lucidm/i2lcd/pictures/6x1.jpg

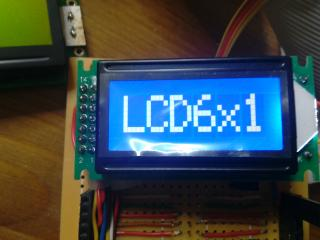
pictures/6x1.jpg
