lucidm/i2lcd/pictures/12x4.jpg

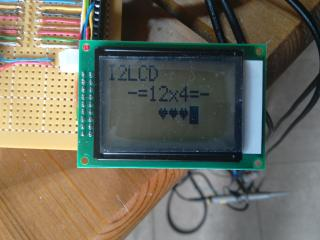
pictures/12x4.jpg
