lucidm/i2lcd/pictures/16x1.jpg

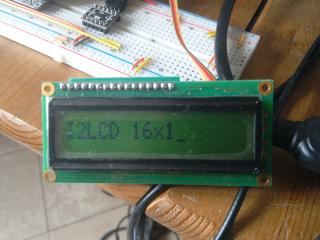
pictures/16x1.jpg
