lucidm/i2lcd/pictures/16x2.jpg

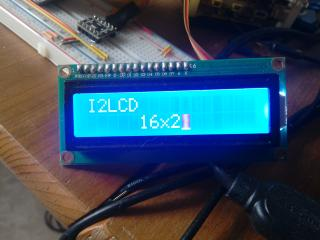
pictures/16x2.jpg
