lucidm/i2lcd/pictures/16x4.jpg

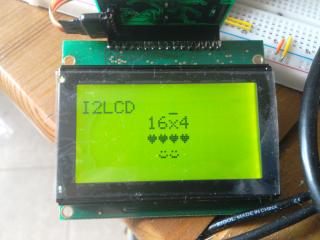
pictures/16x4.jpg
