lucidm/i2lcd/pictures/20x4.jpg

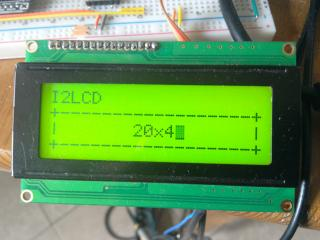
pictures/20x4.jpg
