lucidm/i2lcd/pictures/24x2.jpg

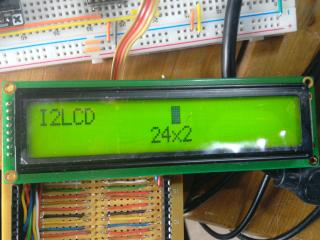
pictures/24x2.jpg
