lucidm/i2lcd/pictures/anano-fritz1.png

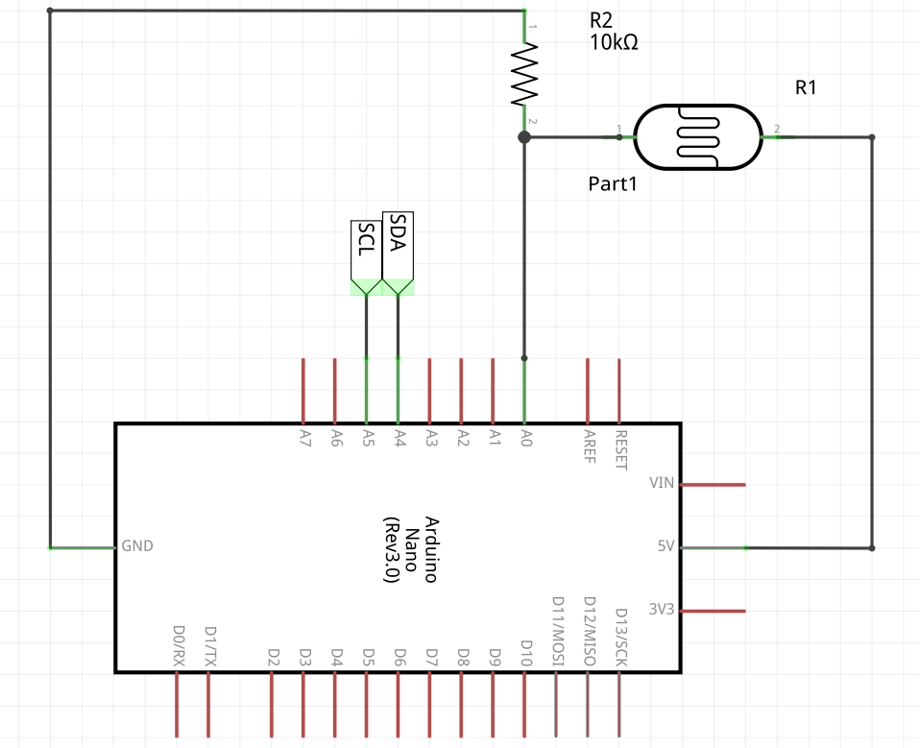
pictures/anano-fritz1.png
