lucidm/i2lcd/pictures/anano-fritz.png

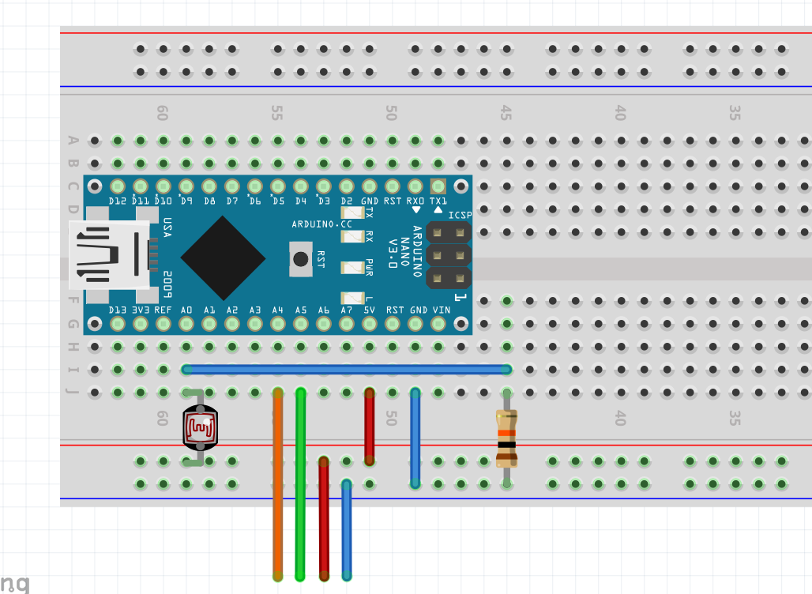
pictures/anano-fritz.png
