lucidm/i2lcd/pictures/backlight-connections4.png

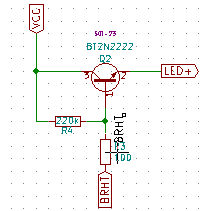
pictures/backlight-connections4.png
