lucidm/i2lcd/pictures/busyflagcir-connections5.png

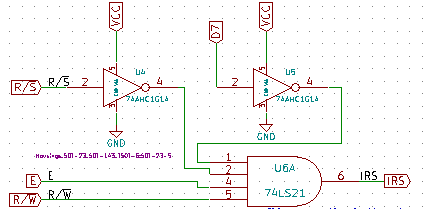
pictures/busyflagcir-connections5.png
