lucidm/i2lcd/pictures/kicad_pcb.png

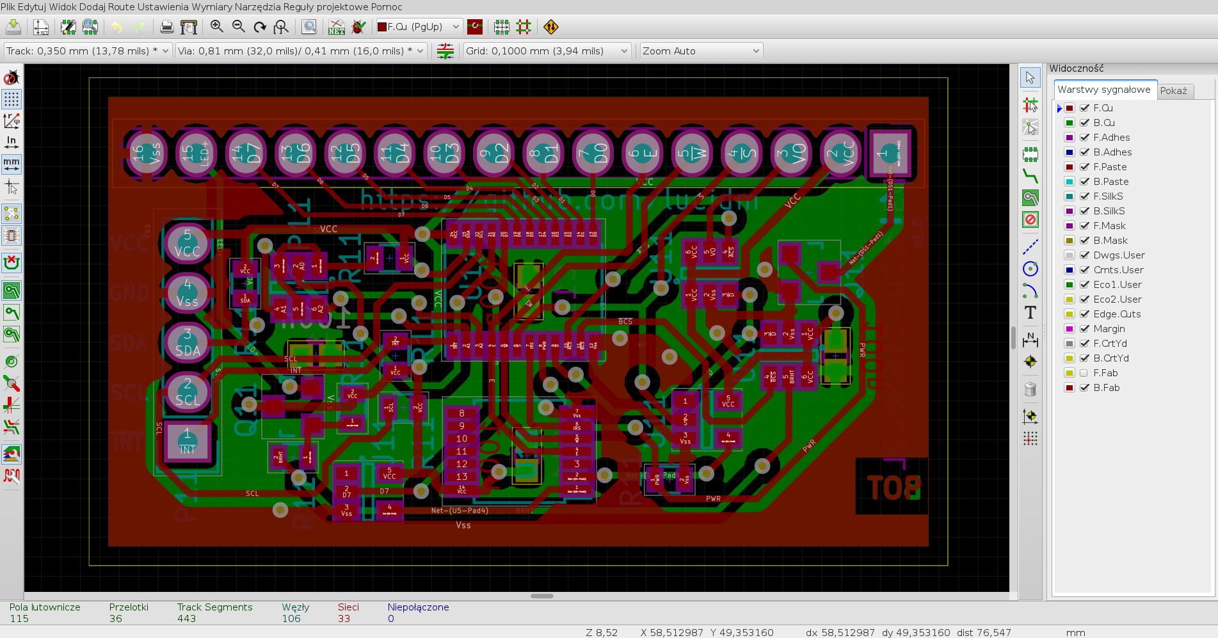
pictures/kicad_pcb.png
