lucidm/i2lcd/pictures/kicad_sch.png

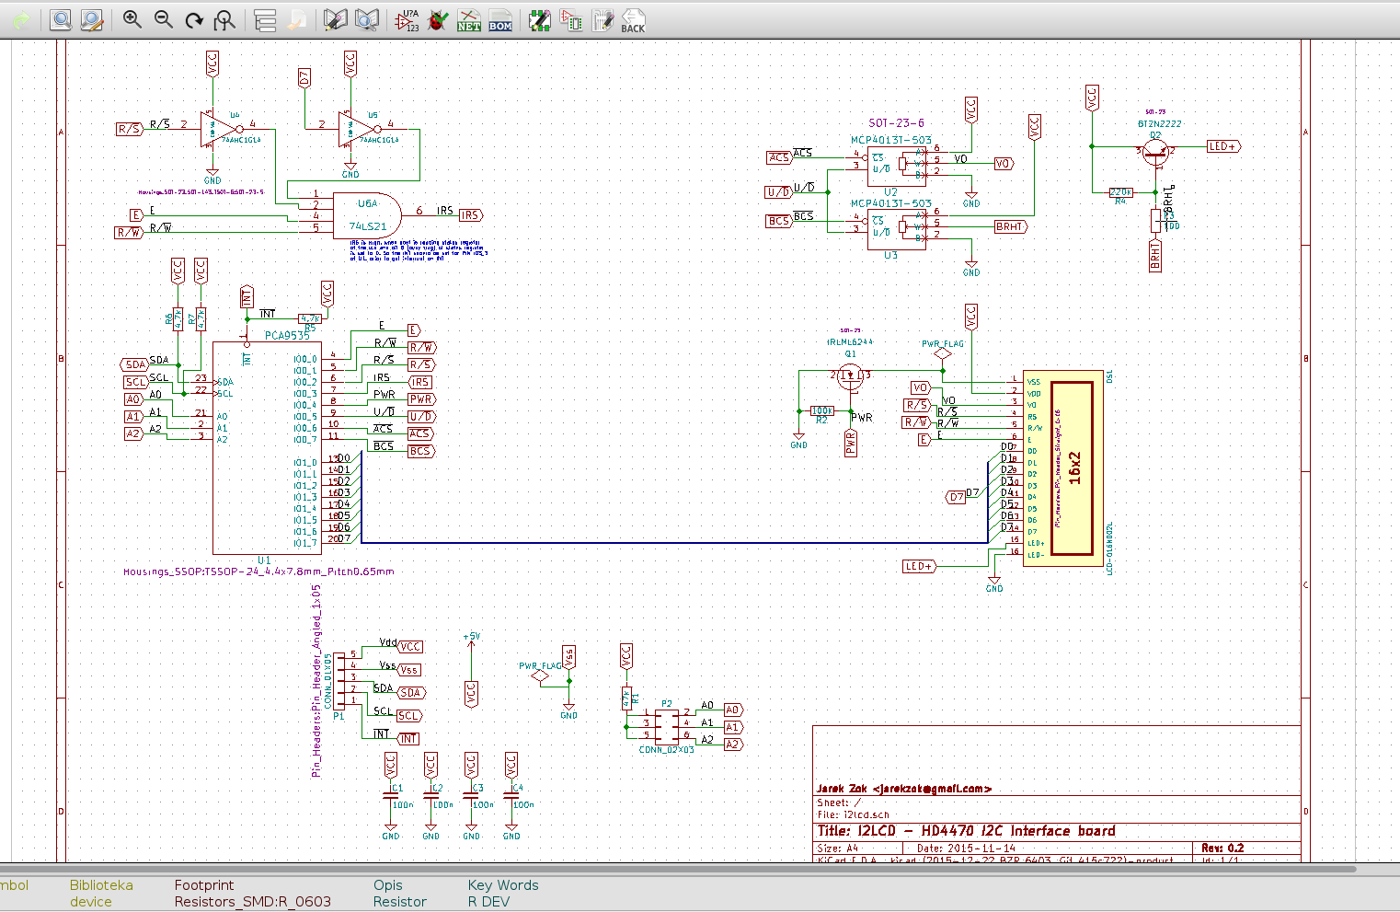
pictures/kicad_sch.png
