lucidm/i2lcd/pictures/lcd-connections2.png

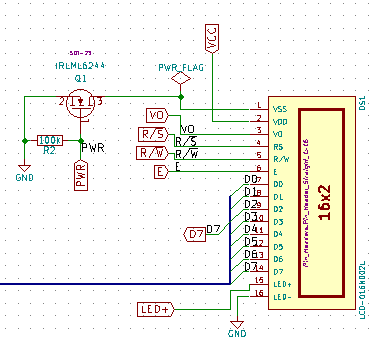
pictures/lcd-connections2.png
