lucidm/i2lcd/pictures/mcp401x-4.png

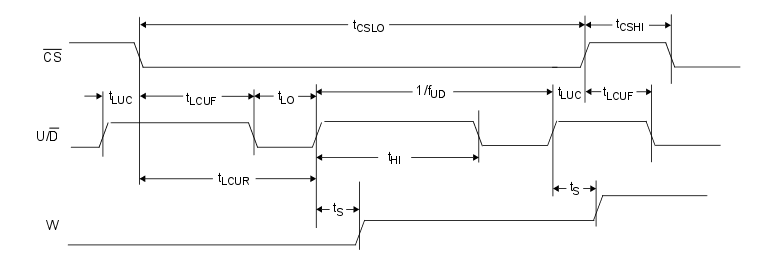
pictures/mcp401x-4.png
