lucidm/i2lcd/pictures/mcp401x-5.png

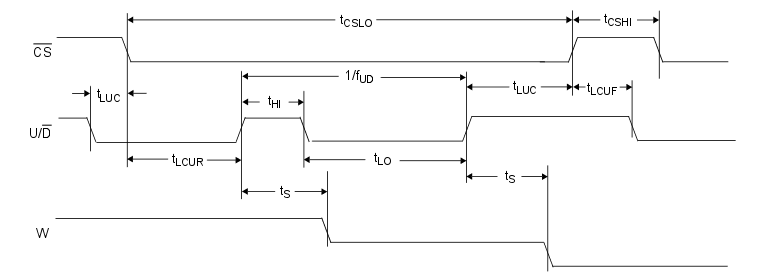
pictures/mcp401x-5.png
