lucidm/i2lcd/pictures/mcp401x-6.png

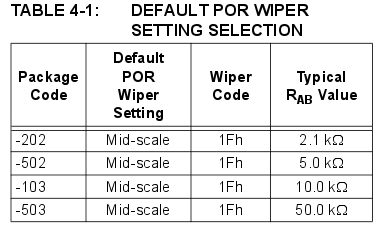
pictures/mcp401x-6.png
