lucidm/i2lcd/pictures/mcp401x-7.png

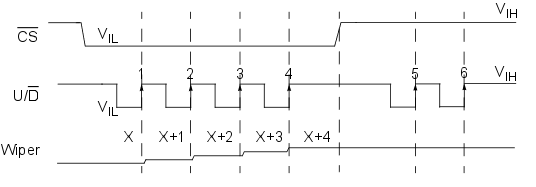
pictures/mcp401x-7.png
