lucidm/i2lcd/pictures/NotLCD.jpg

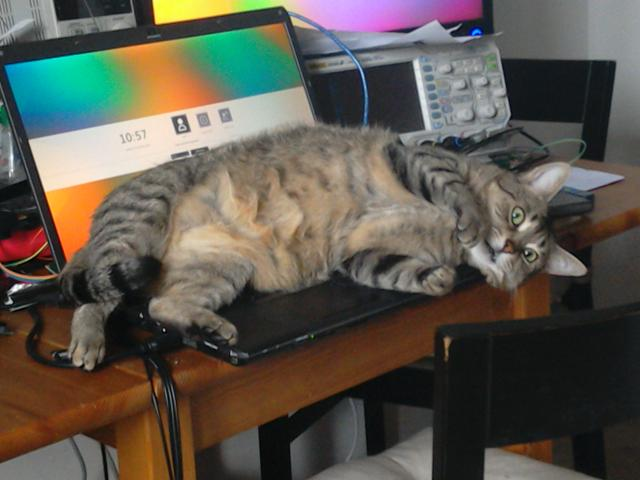
pictures/NotLCD.jpg
