lucidm/i2lcd/pictures/pca9535-1.png

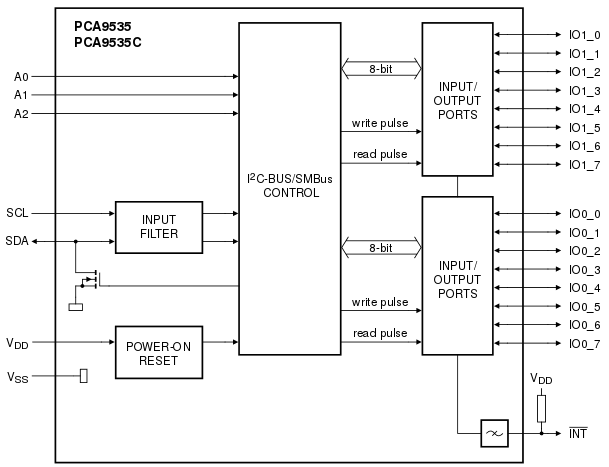
pictures/pca9535-1.png
