lucidm/i2lcd/pictures/pca9535-2.png

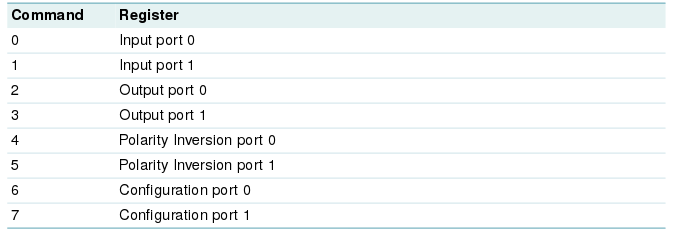
pictures/pca9535-2.png
