lucidm/i2lcd/pictures/pca9535-3.png

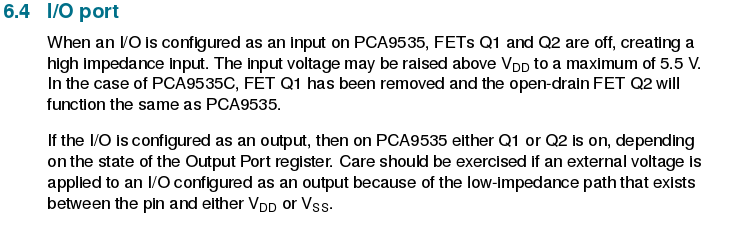
pictures/pca9535-3.png
