lucidm/i2lcd/pictures/pca-connections1.png

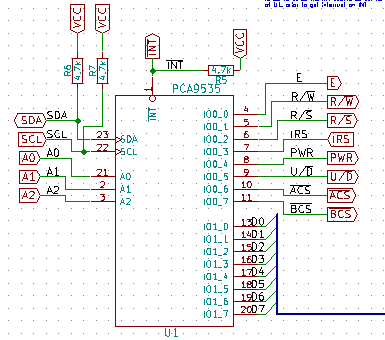
pictures/pca-connections1.png
