lucidm/i2lcd/kicad/i2lcd/i2lcd.sch

## KiCad design kicad/i2lcd/i2lcd.sch (2016-02-21)

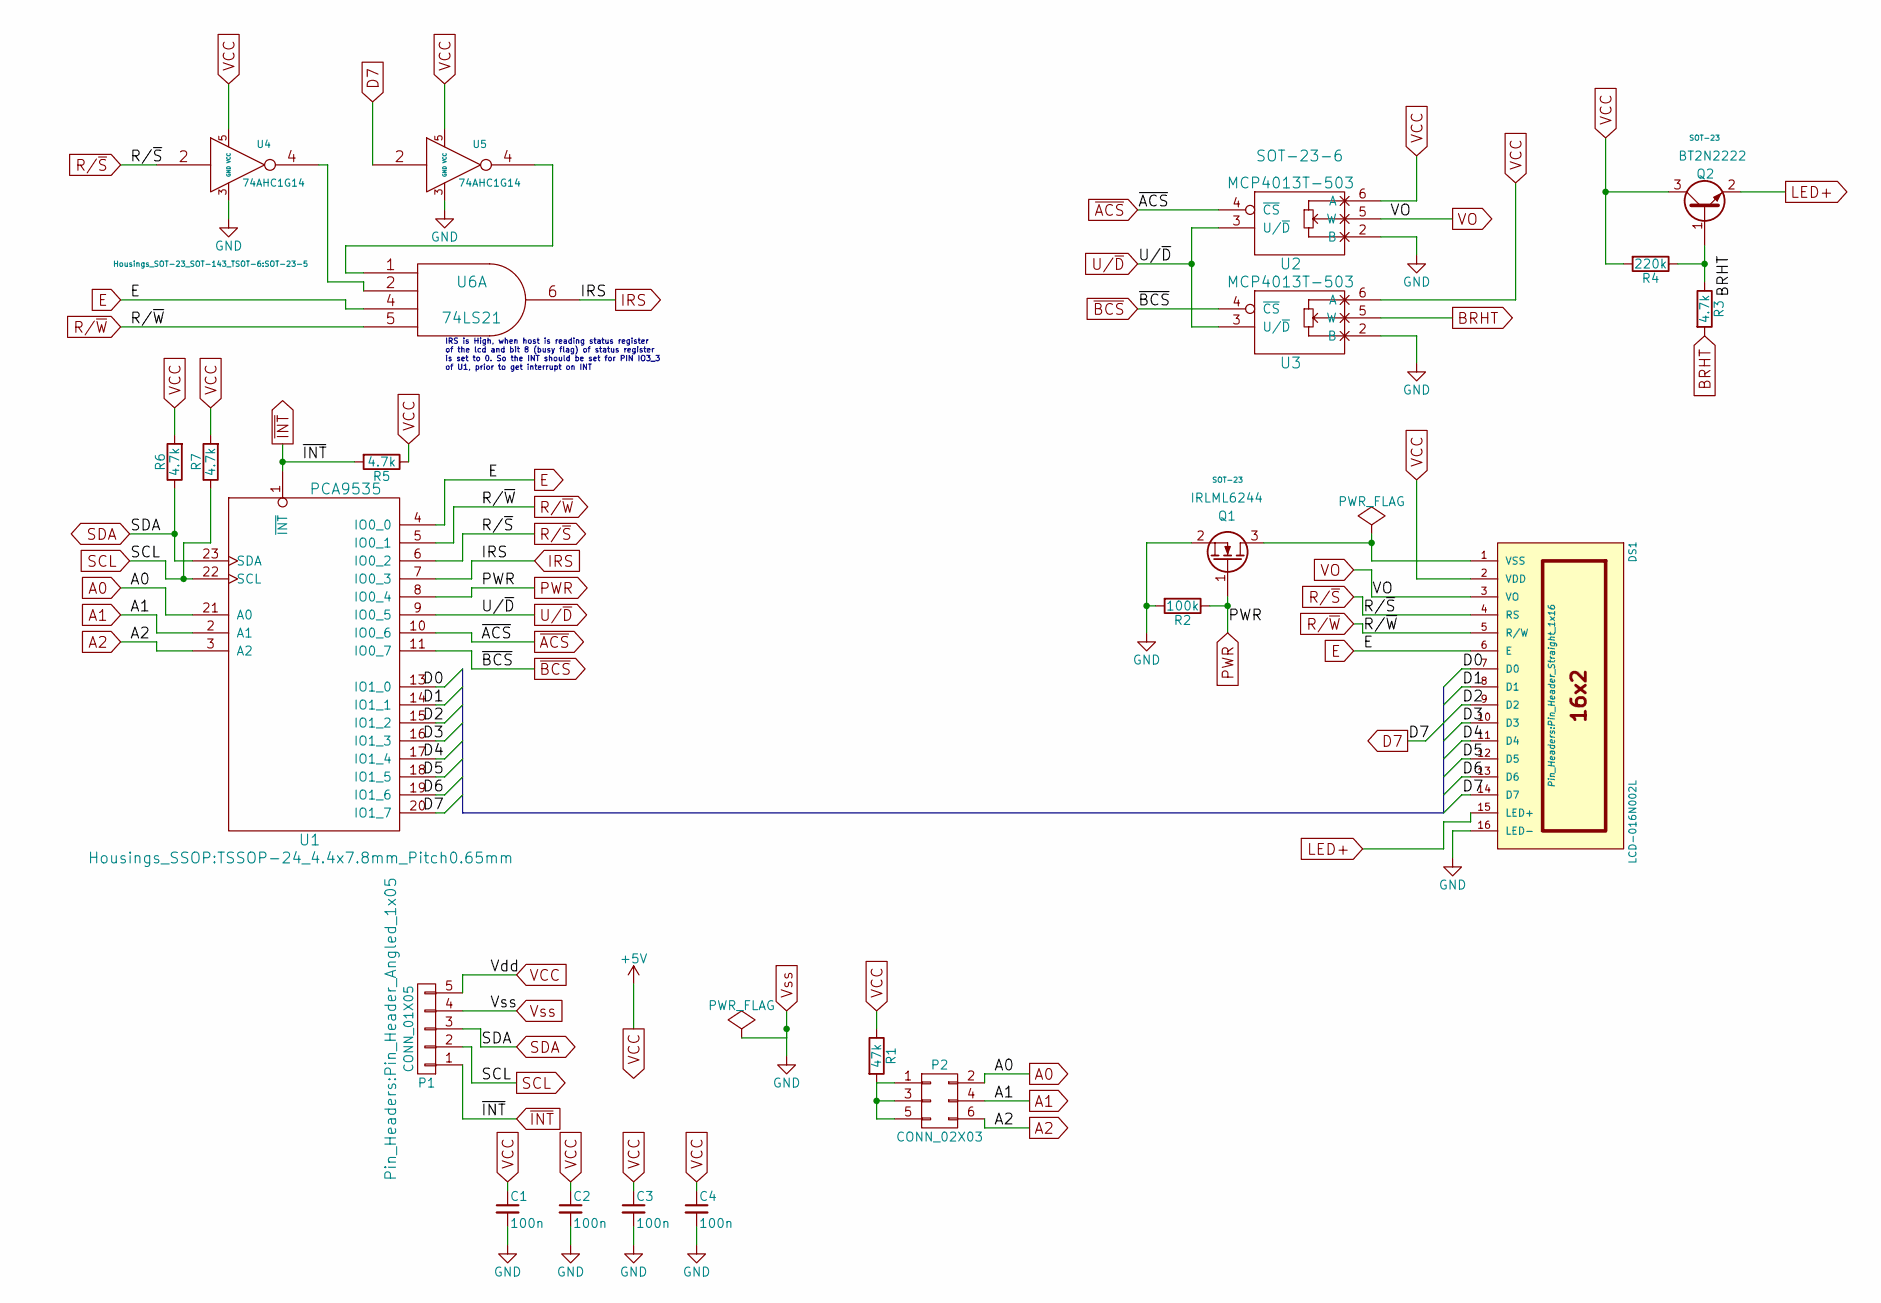
[picture p30: schematic i2lcd.sch]

Parts:
C1, C2, C3, C4: 100n; C_0603
DS1: LCD-016N002L; Pin_Header_Straight_1x16
P1: CONN_01X05; Pin_Header_Angled_1x05
P2: CONN_02X03; SOT-23-6
Q1: IRLML6244; SOT-23
Q2: BT2N2222; SOT-23
R1: 47k; R_0603
R2: 100k; R_0603
R3, R5, R6, R7: 4.7k; R_0603
R4: 220k; R_0603
U1: PCA9535; TSSOP-24_4.4x7.8mm_Pitch0.65mm
U2, U3: MCP4013T-503; SOT-23-6
U4, U5: 74AHC1G14; SOT-23-5
U6: 74LS21; TSSOP-14_4.4x5mm_Pitch0.65mm

Connections:
+5V: C1.1, C2.1, C3.1, C4.1, DS1.2 (VDD), P1.5, Q2.3 (C), R1.1, R4.2, R5.1, R6.2, R7.2, U2.6 (A), U3.6 (A), U4.5 (VCC), U5.5 (VCC)
A0: P2.2, U1.21 (A0)
A1: P2.4, U1.2 (A1)
A2: P2.6, U1.3 (A2)
BRHT: R3.2, U3.5 (W)
D0: DS1.7 (D0), U1.13 (IO1_0)
D1: DS1.8 (D1), U1.14 (IO1_1)
D2: DS1.9 (D2), U1.15 (IO1_2)
D3: DS1.10 (D3), U1.16 (IO1_3)
D4: DS1.11 (D4), U1.17 (IO1_4)
D5: DS1.12 (D5), U1.18 (IO1_5)
D6: DS1.13 (D6), U1.19 (IO1_6)
D7: DS1.14 (D7), U1.20 (IO1_7), U5.2
E: DS1.6 (E), U1.4 (IO0_0), U6.4
GND: C1.2, C2.2, C3.2, C4.2, DS1.16 (LED-), P1.4, Q1.2 (S), R2.2, U2.2 (B), U3.2 (B), U4.3 (GND), U5.3 (GND)
IRS: U1.7 (IO0_3), U6.6
LED+: DS1.15 (LED+), Q2.2 (E)
unnamed: DS1.1 (VSS), Q1.3 (D)
unnamed: P2.1, P2.3, P2.5, R1.2
unnamed: Q2.1 (B), R3.1, R4.1
unnamed: U4.4, U6.2
unnamed: U5.4, U6.1
PWR: Q1.1 (G), R2.1, U1.8 (IO0_4)
R/~S: DS1.4 (RS), U1.6 (IO0_2), U4.2
R/~W: DS1.5 (R/W), U1.5 (IO0_1), U6.5
SCL: P1.2, R7.1, U1.22 (SCL)
SDA: P1.3, R6.1, U1.23 (SDA)
U/~D: U1.9 (IO0_5), U2.3 (U/~D), U3.3 (U/~D)
VO: DS1.3 (VO), U2.5 (W)
~ACS: U1.10 (IO0_6), U2.4 (~CS)
~BCS: U1.11 (IO0_7), U3.4 (~CS)
~INT: P1.1, R5.2, U1.1 (~INT)

Notes on the sheet:
IRS is High, when host is reading status register of the lcd and bit 8 (busy flag) of status register is set to 0. So the INT should be set for PIN IO3_3 of U1, prior to get interrupt on INT
